Neumi/open_echo/documentation/images/all-in-one-x1.jpg

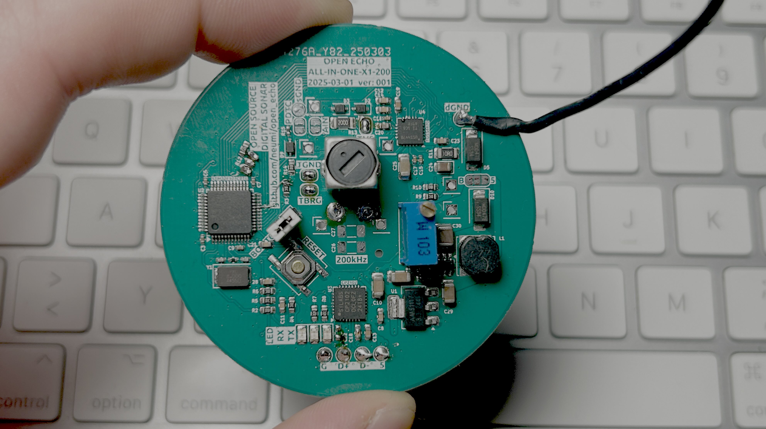
documentation/images/all-in-one-x1.jpg
