Neumi/open_echo/documentation/images/all_in_pcb.png

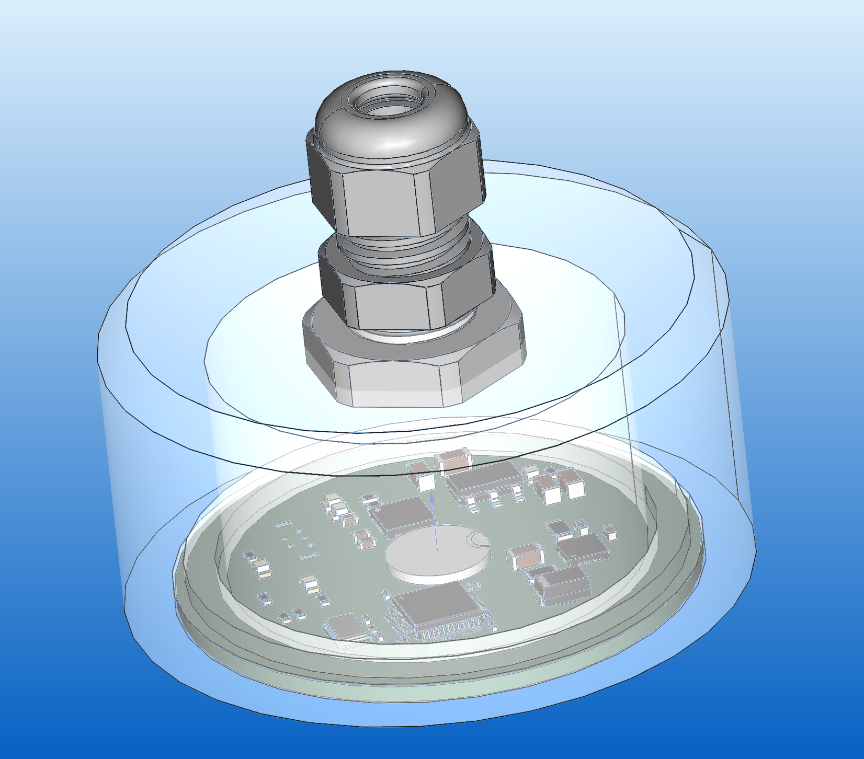
documentation/images/all_in_pcb.png
