Neumi/open_echo/documentation/images/cover.JPG

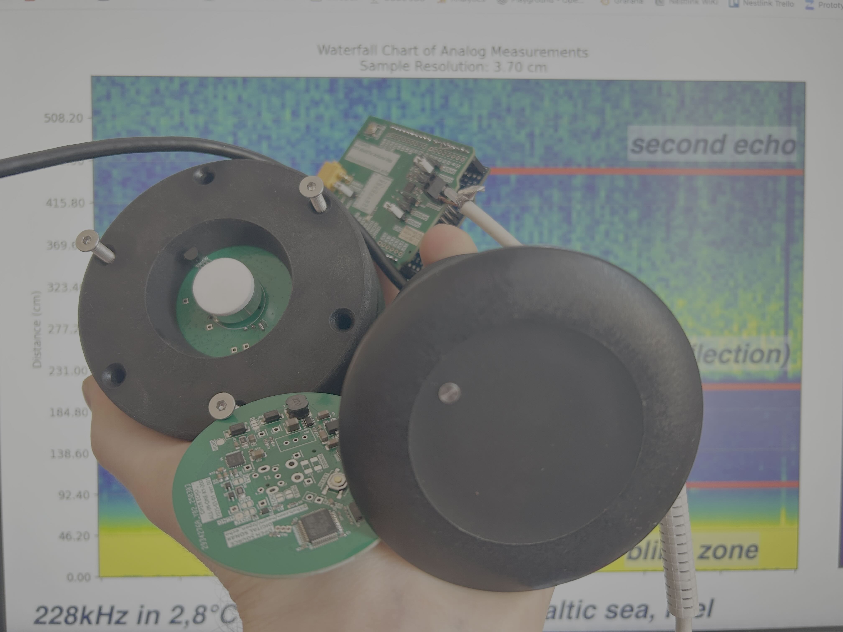
documentation/images/cover.JPG
