Neumi/open_echo/documentation/images/iboating_NMEA_DBT.jpg

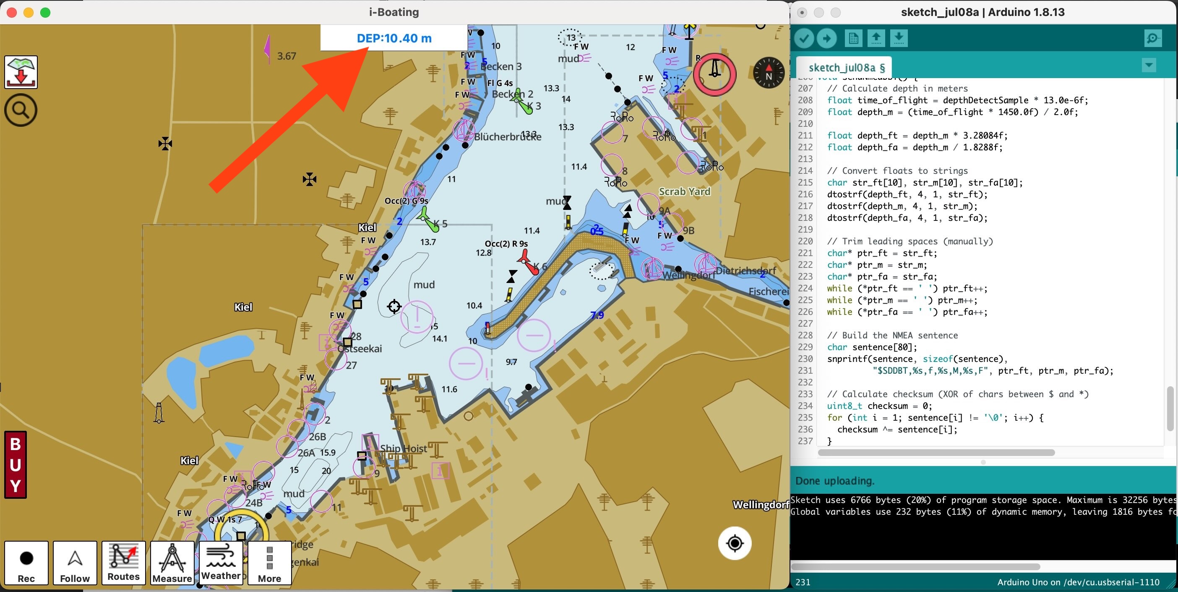
documentation/images/iboating_NMEA_DBT.jpg
