Neumi/open_echo/documentation/images/open_echo_python.png

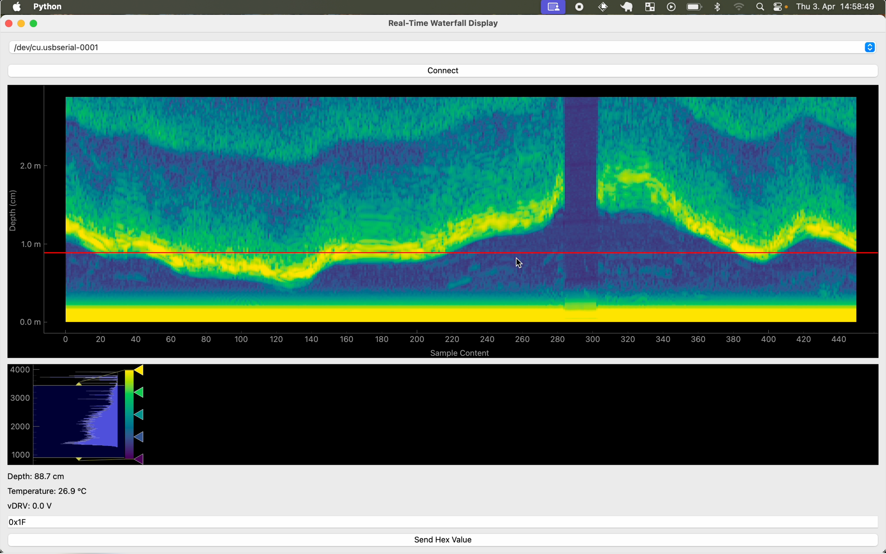
documentation/images/open_echo_python.png
