Neumi/open_echo/documentation/images/pyQT_software.png

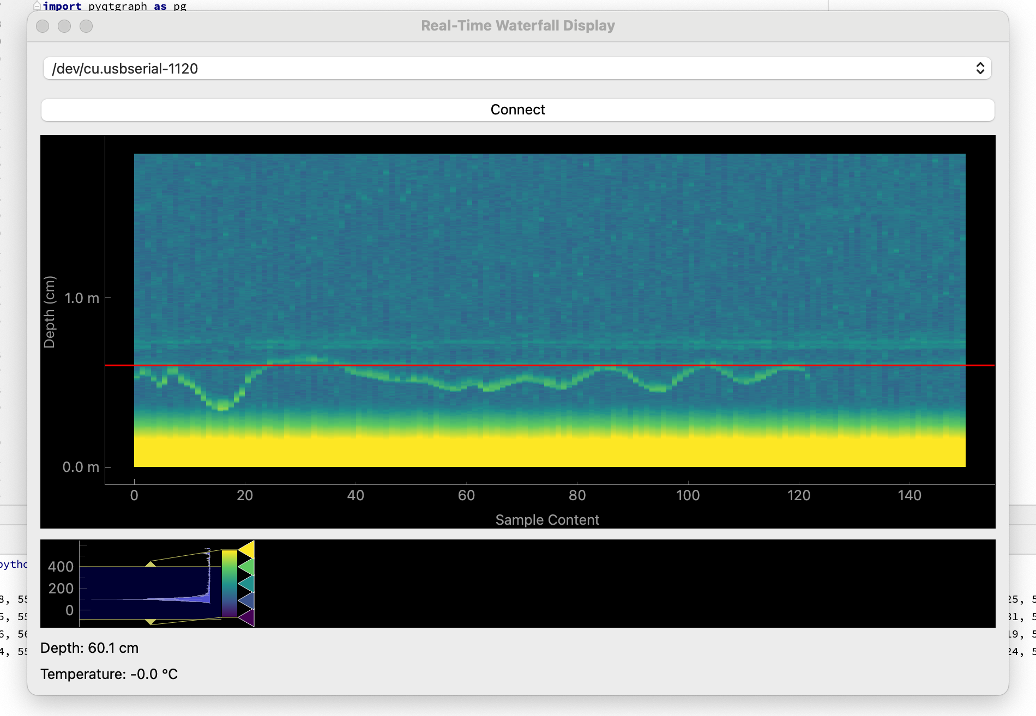
documentation/images/pyQT_software.png
