Neumi/open_echo/documentation/images/TUSS4470_add_MT3608.jpg

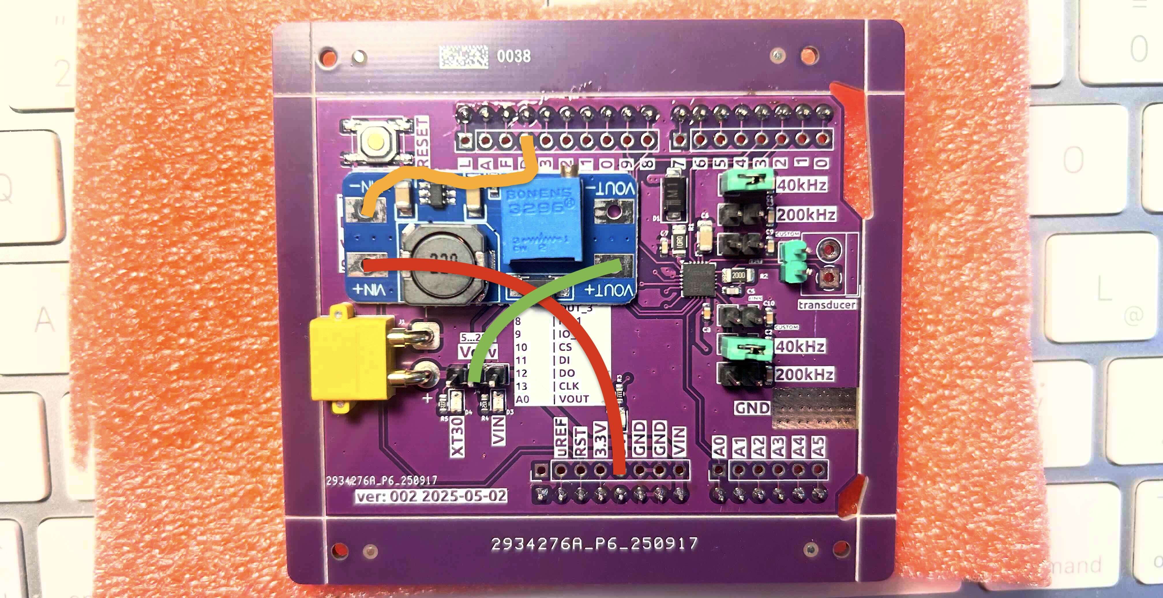
documentation/images/TUSS4470_add_MT3608.jpg
