Neumi/open_echo/reverse_engineering/images/back.JPG

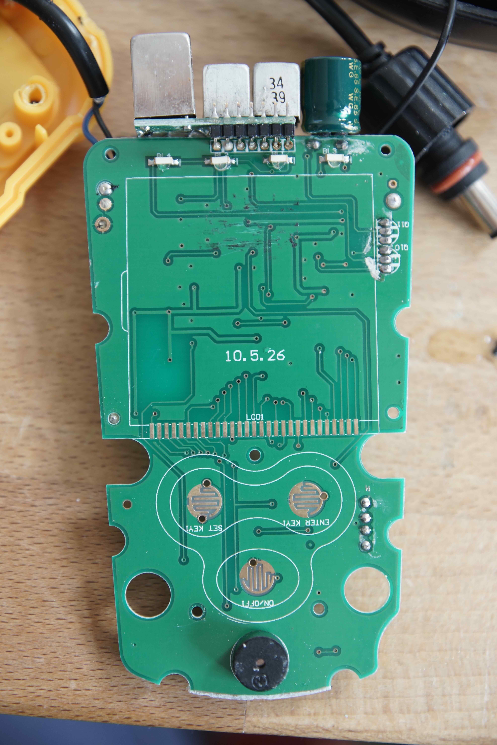
reverse_engineering/images/back.JPG
