Neumi/open_echo/TUSS4470_shield_002/TUSS4470_shield_hardware/images/echos.jpg

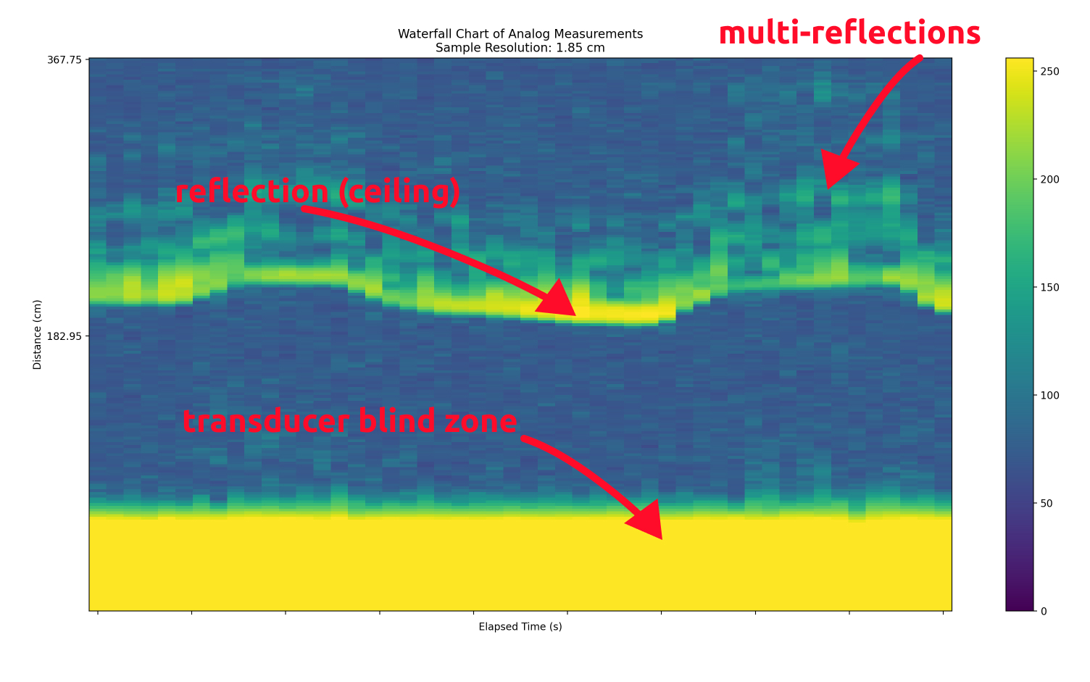
TUSS4470_shield_002/TUSS4470_shield_hardware/images/echos.jpg
