Neumi/open_echo/documentation/images/baltic_sea_tests/seaweed_fish.png

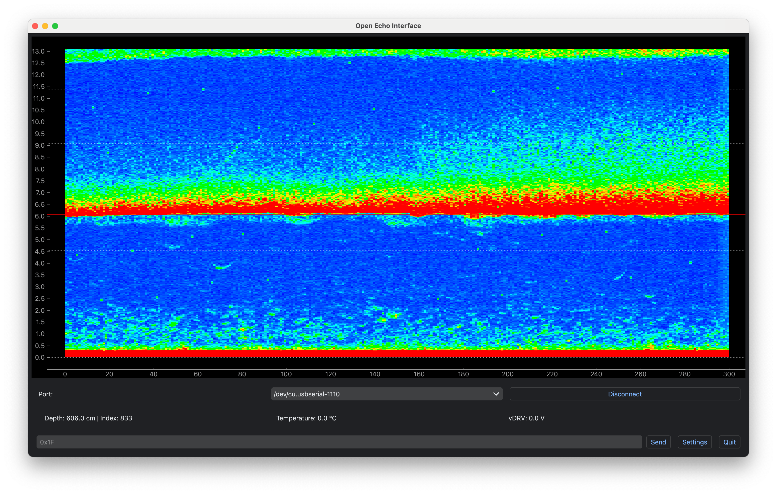
documentation/images/baltic_sea_tests/seaweed_fish.png
