Neumi/open_echo/documentation/images/baltic_test200khz.jpg

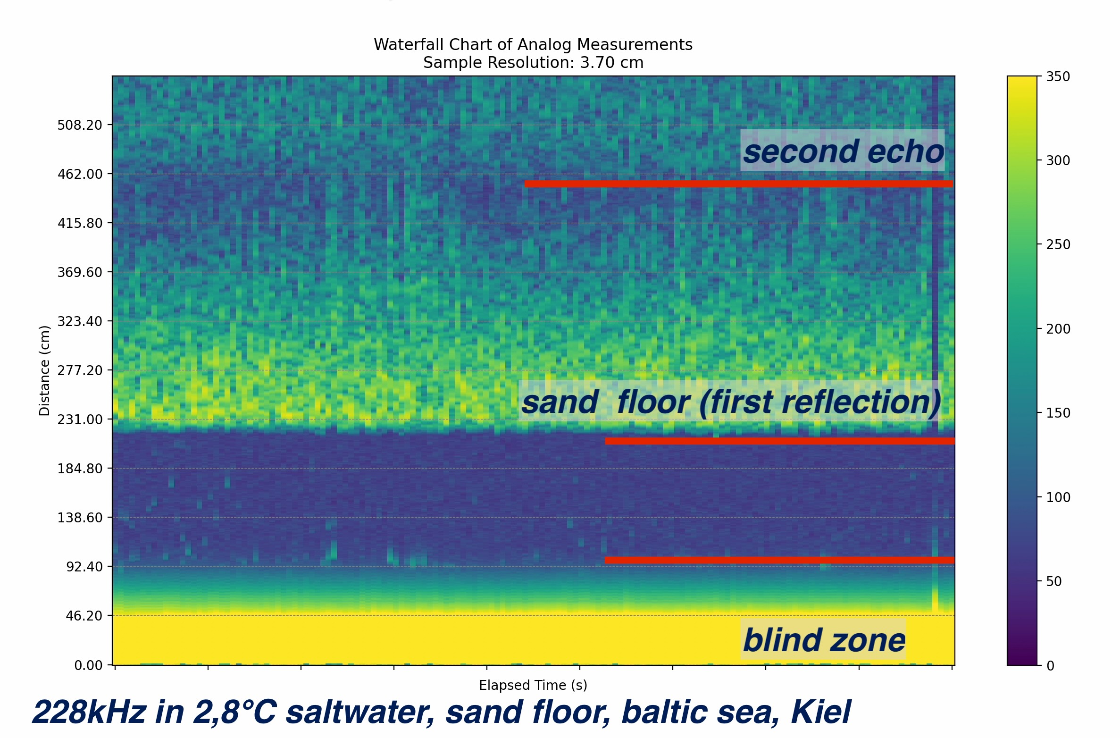
documentation/images/baltic_test200khz.jpg
