Neumi/open_echo/documentation/images/lake_test200kHz.jpg

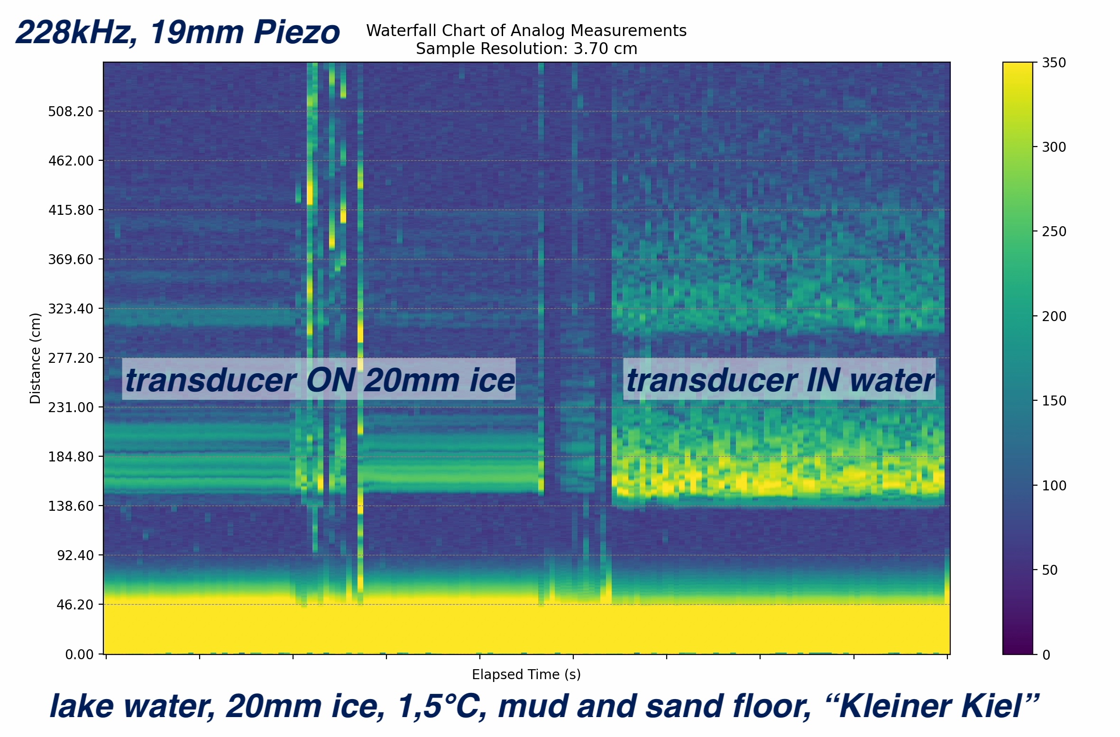
documentation/images/lake_test200kHz.jpg
